atomic14/kicad-esp32-dev-boards/scripts/make.py

#!/usr/bin/env python3
"""One front door for the whole pipeline: clean -> build -> route -> render -> fab.

This is THE command to run. It chains the per-stage orchestrators (each of
which still works standalone):

  clean.py          remove prior generated output      (opt-in: --clean)
  build_all.py      schematic + PCB + ERC, every module (default ON)
  route_all.py      autoroute + DRC, every board        (default ON)
  render_boards.py  3D montages into build/             (opt-in: --render)
  fab_all.py        Gerber + drill zips into out/        (opt-in: --fab)

Run resolve_library.py once per machine first (creates library.json).

Usage:
  make.py                 # build + route every curated module
  make.py --clean         # wipe prior output first
  make.py --render        # also render the 3D montages at the end
  make.py --fab           # also export fab zips (Gerbers + drill) per module
  make.py --all           # clean + build + route + render + fab
  make.py --no-route      # build only (stop before routing)
  make.py --diff          # forward diff-pair routing to route_all
"""
from __future__ import annotations
import argparse
import json
import subprocess
import sys
from pathlib import Path

REPO = Path(__file__).resolve().parent.parent
SCRIPTS = REPO / "scripts"
PY = [sys.executable]


def check_library() -> str | None:
    """Validate library.json exists AND its paths still resolve. Returns an
    error message (with the fix) if not usable, else None. Catches both the
    fresh-machine case and the stale-json case (KiCad upgraded out from under
    paths recorded for an older version)."""
    lib = REPO / "library.json"
    fix = "run: uv run python scripts/resolve_library.py"
    if not lib.exists():
        return f"library.json missing — {fix}"
    try:
        info = json.loads(lib.read_text())
    except (json.JSONDecodeError, OSError) as e:
        return f"library.json unreadable ({e}) — {fix}"
    for key in ("kicad_cli", "symbol_lib", "footprint_lib", "kicad_symbols_dir"):
        p = info.get(key)
        if not p or not Path(p).exists():
            return (
                f"library.json points to a missing path ({key}={p!r}) — likely a "
                f"KiCad upgrade/reinstall since it was generated. {fix}"
            )
    return None


def stage(title, script, *args):
    """Run a stage script live (inherit stdio). Return its exit code."""
    print(f"\n{'=' * 60}\n== {title}\n{'=' * 60}", flush=True)
    return subprocess.run(PY + [str(SCRIPTS / script), *args]).returncode


def main(argv):
    ap = argparse.ArgumentParser()
    ap.add_argument("--clean", action="store_true", help="wipe prior output first")
    ap.add_argument("--no-route", action="store_true", help="build only; stop before routing")
    ap.add_argument("--render", action="store_true", help="also render 3D montages at the end")
    ap.add_argument("--fab", action="store_true", help="also export fab zips (Gerbers + drill)")
    ap.add_argument("--all", action="store_true", help="clean + build + route + render + fab")
    ap.add_argument("--no-diff", dest="diff", action="store_false",
                    help="route D+/D- single-ended (diff-pair is the default)")
    ap.set_defaults(diff=True)
    args = ap.parse_args(argv)

    lib_err = check_library()
    if lib_err:
        print(f"ERROR: {lib_err}", file=sys.stderr)
        return 1

    do_clean = args.clean or args.all
    do_route = not args.no_route or args.all
    do_render = args.render or args.all
    do_fab = args.fab or args.all

    if do_clean:
        if stage("CLEAN", "clean.py"):
            return 1

    # build_all already cleans when asked; we cleaned above, so don't double up.
    if stage("BUILD + VALIDATE", "build_all.py"):
        print("\nBuild failed — stopping before routing.", file=sys.stderr)
        return 1

    if do_route:
        route_args = [] if args.diff else ["--no-diff"]
        if stage("ROUTE + DRC", "route_all.py", *route_args):
            print("\nRouting reported failures (see summary above).", file=sys.stderr)
            # keep going to render if requested — a partial route is still worth seeing
            rc = 1
        else:
            rc = 0
    else:
        rc = 0

    if do_render:
        if stage("RENDER", "render_boards.py"):
            return 1

    if do_fab:
        if stage("FAB EXPORT (Gerbers + drill)", "fab_all.py"):
            return 1

    return rc


if __name__ == "__main__":
    raise SystemExit(main(sys.argv[1:]))
